antarcticlion/RGBHV_RGBS_CONV/10B_SIDEA.png

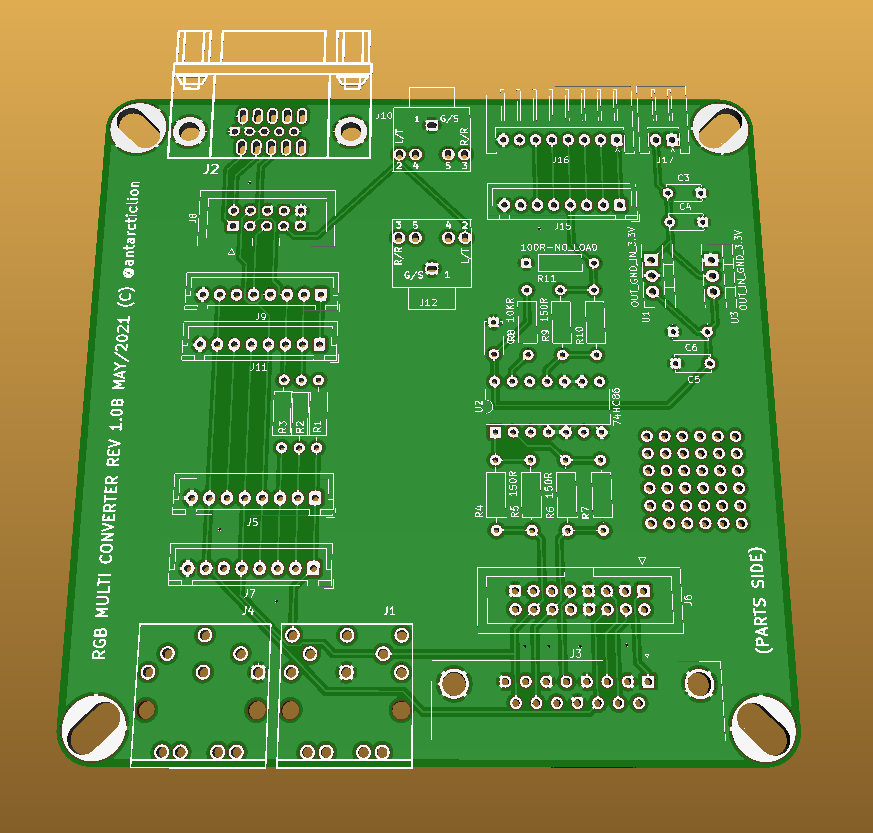
10B_SIDEA.png
