antarcticlion/RGBHV_RGBS_CONV/10C_SIDEA.png

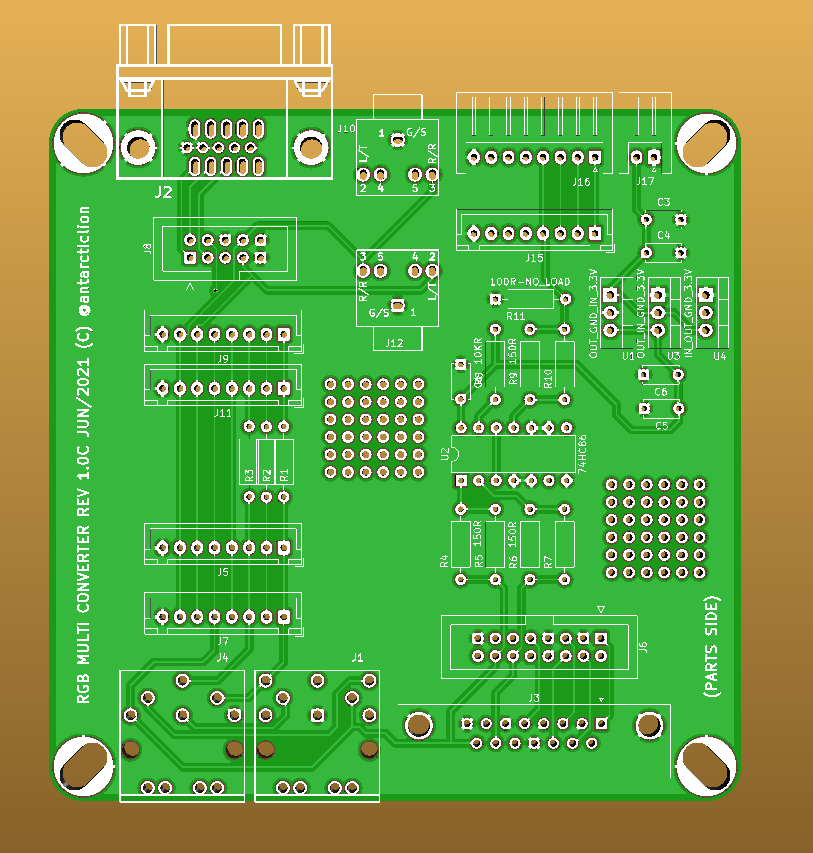
10C_SIDEA.png
