antarcticlion/RGBHV_RGBS_CONV/10C_SIDEB.png

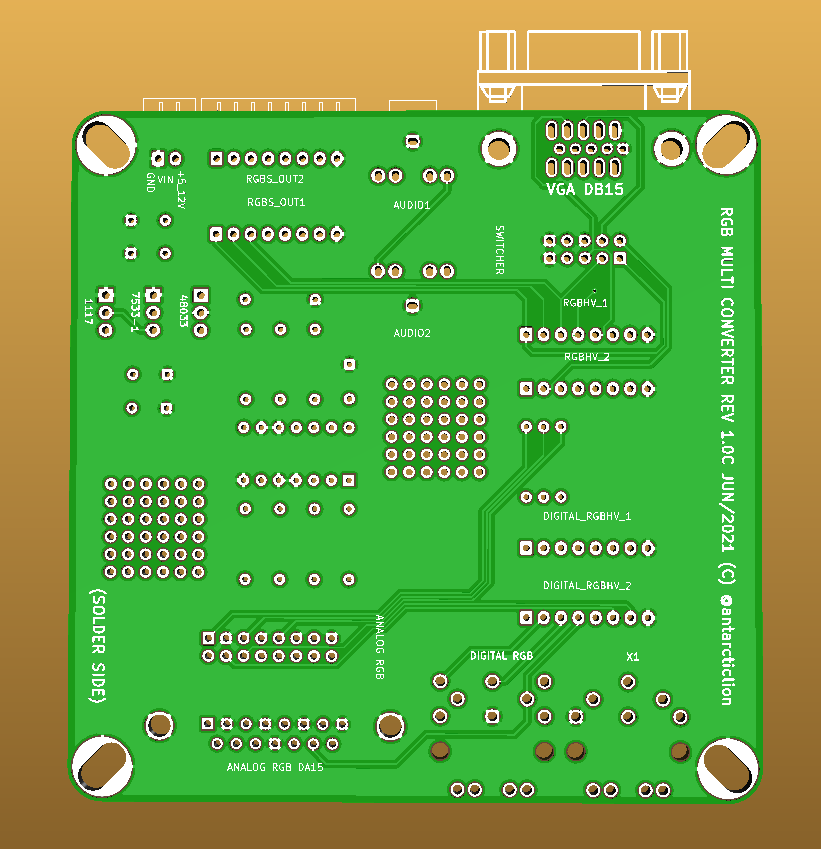
10C_SIDEB.png
