antarcticlion/RGBHV_RGBS_CONV/images/Rev.1.5/Rev1.5_EXTRA1_SIDE_A.png

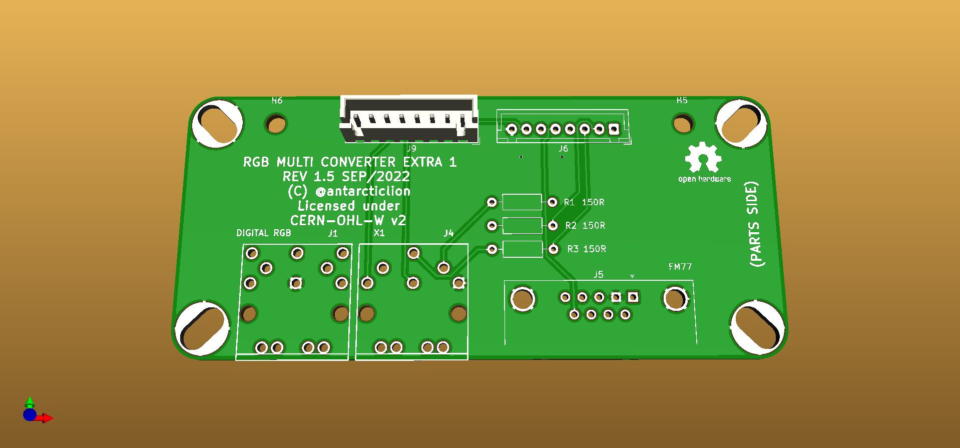
images/Rev.1.5/Rev1.5_EXTRA1_SIDE_A.png
