antarcticlion/RGBHV_RGBS_CONV/pcb_art_rev5b_omote.png

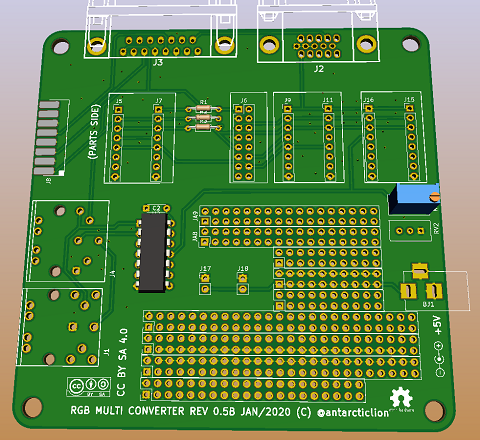
pcb_art_rev5b_omote.png
