antarcticlion/RGBHV_RGBS_CONV/pcb_art_rev5b_ura.png

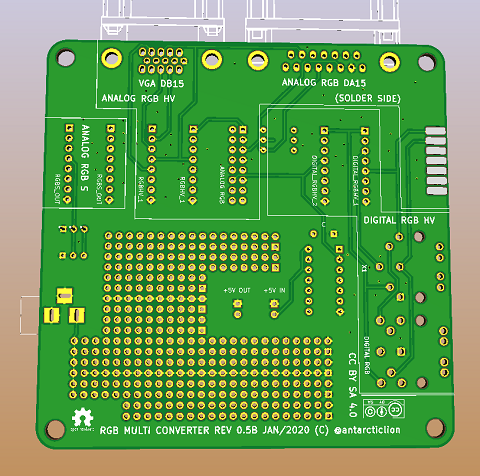
pcb_art_rev5b_ura.png
