antarcticlion/RGBHV_RGBS_CONV/pcb_art_rev5omote.jpg

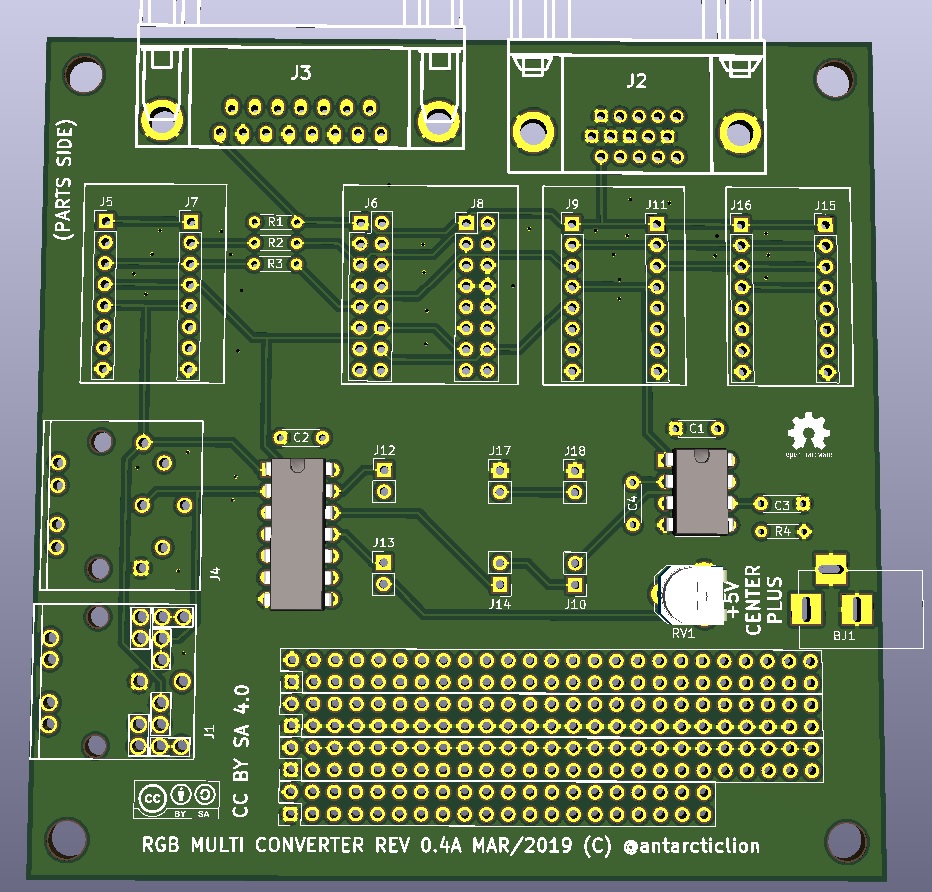
pcb_art_rev5omote.jpg
