antarcticlion/RGBHV_RGBS_CONV/rev4_pcb_photo.jpg

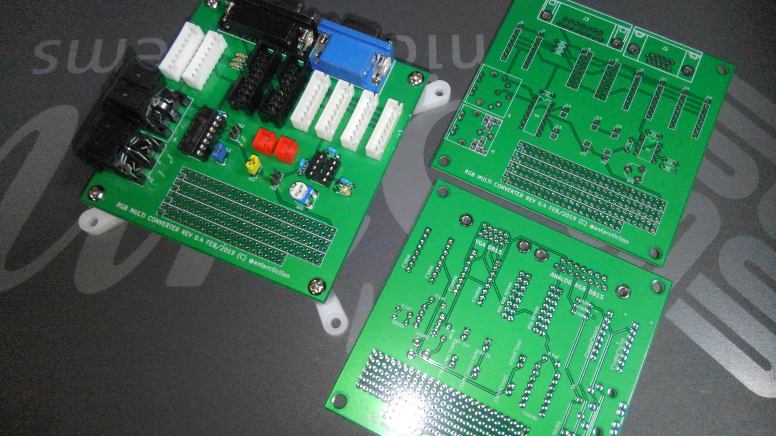
rev4_pcb_photo.jpg
