antarcticlion/RGBHV_RGBS_CONV/rev5a_photo.jpg

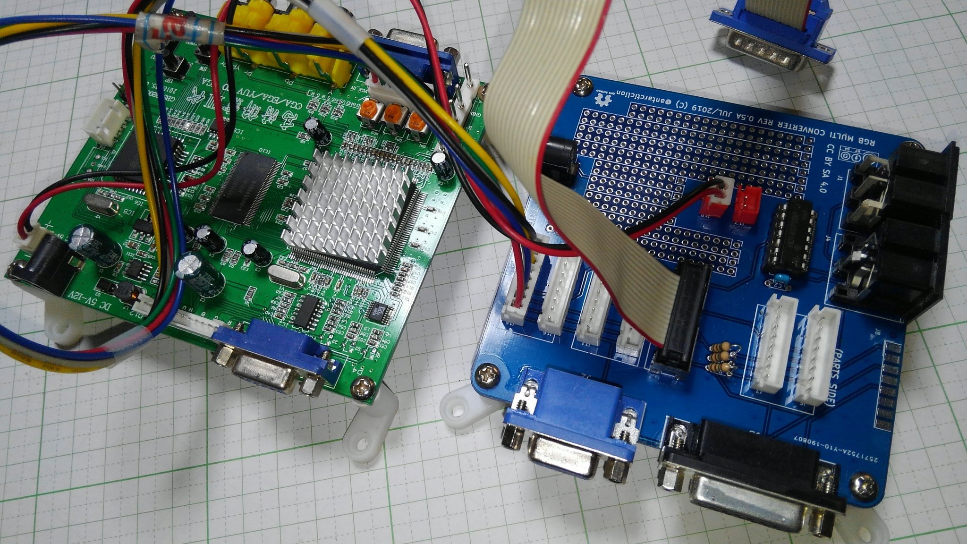
rev5a_photo.jpg
