antarcticlion/RGBHV_RGBS_CONV/REV10B1.jpg

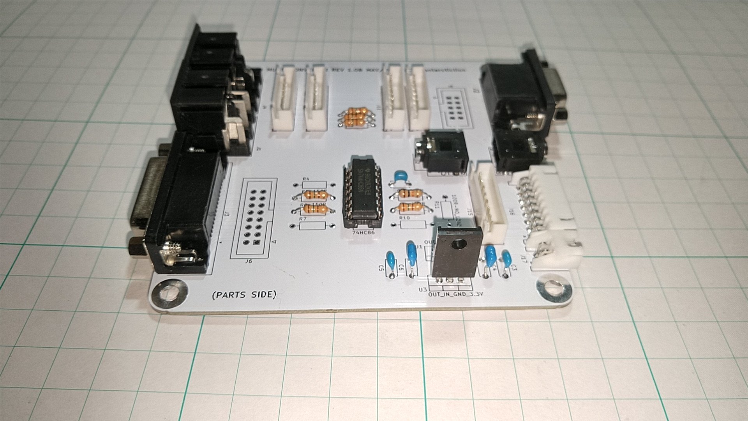
REV10B1.jpg
