antarcticlion/RGBHV_RGBS_CONV/REV10B2.jpg

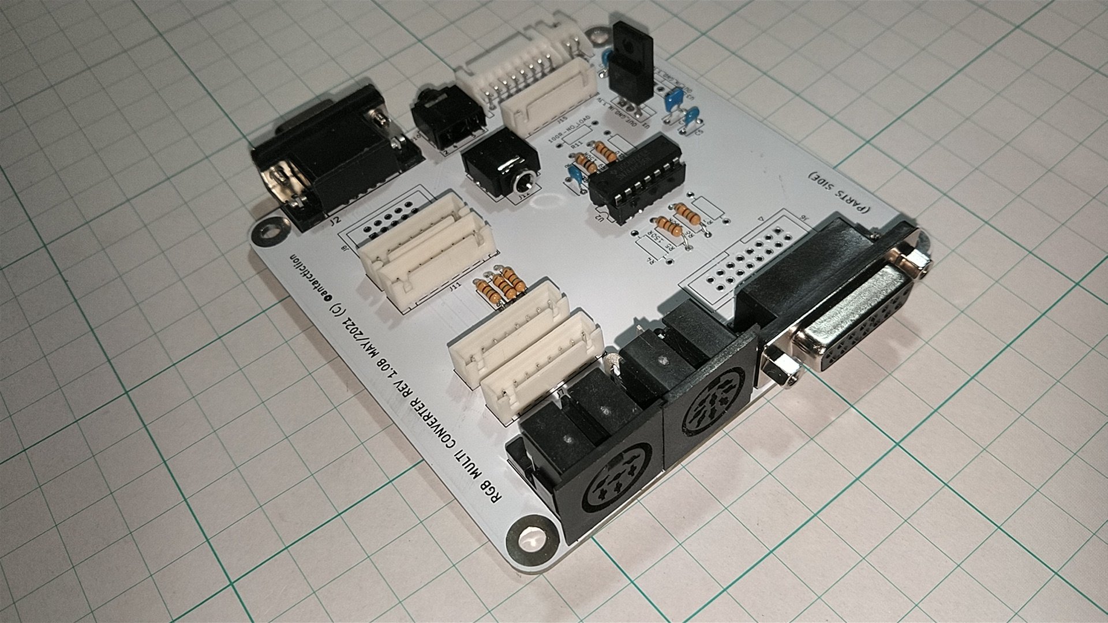
REV10B2.jpg
